0xMartin/QCW-Tesla-Coil/graphs/GDT/img1.bmp

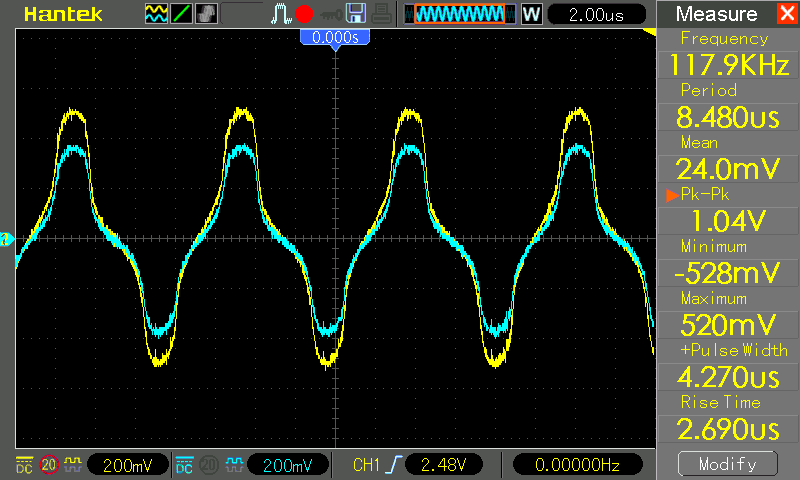
graphs/GDT/img1.bmp
