0xMartin/QCW-Tesla-Coil/graphs/GDT/img2.bmp

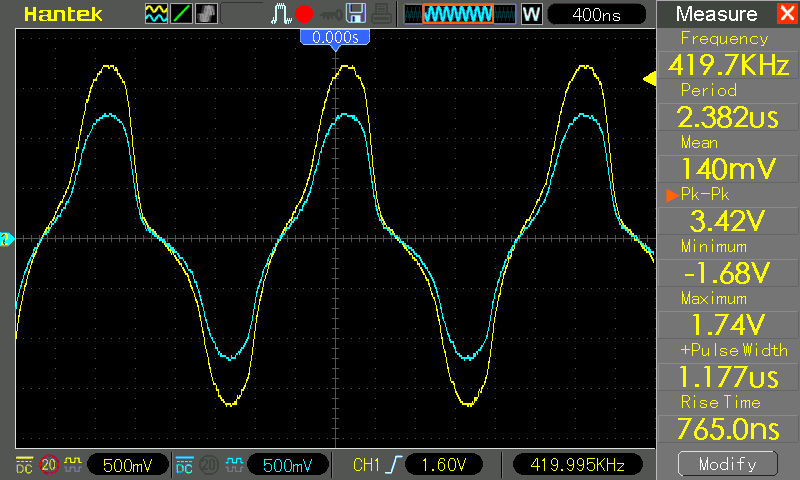
graphs/GDT/img2.bmp
