0xMartin/QCW-Tesla-Coil/images/img1.jpg

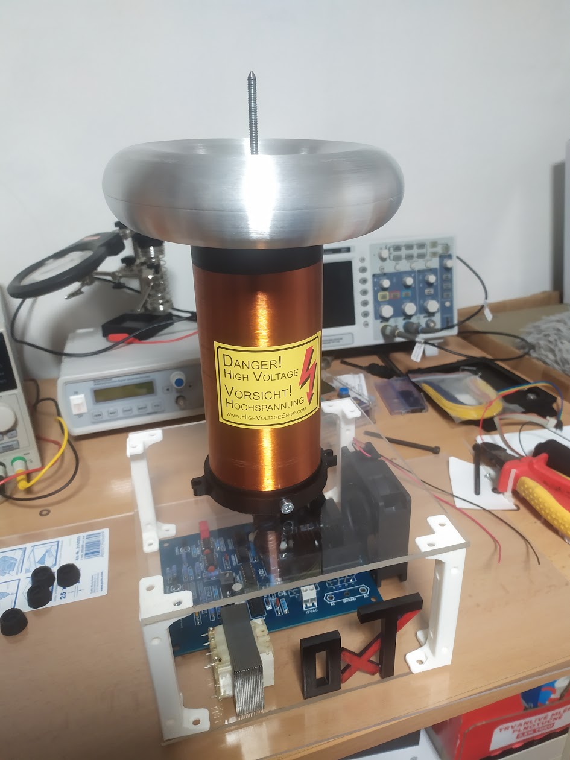
images/img1.jpg
